chris-markus/cue-lights/controller/strings.h

// =====================================================
// Copyright (C) 2020 Christopher Markus 
// www.chrismarkus.me
// This software is licensed under the GNU GPLv3 License
// =====================================================

#ifndef STRINGS_H
#define STRINGS_H

// Strings file for controller UI
#define STR_SPLASH "Tufts Drama + Dance"

#define STR_PRESSFORMENU "Press for main menu"

#define STR_ON "On"
#define STR_OFF "Off"

#define STR_LIGHTS_STATUS "%d lights connected"

// menu strings:
#define STR_MENU_MAIN "Settings"

#define STR_BACK_BUTTON "< Back"
#define STR_CLOSE_BUTTON "X Close"

#define STR_PANEL_LIGHTS "Controller Lights"
#define STR_STATION_LIGHTS "Cue Lights"
#define STR_BRIGHTNESS "Brightness"

#define STR_STATION_I "Station %d"

#define STR_TEST_STATIONS "Test Station(s)"
#define STR_TEST_ALL_STATIONS "Test All"
#define STR_TEST_ONE_STATION "Test One"

#define STR_STBY_COLOR "Standby Color"
#define STR_GO_COLOR "Go Color"

#define STR_RED "Red"
#define STR_GREEN "Green"
#define STR_BLUE "Blue"

#define STR_NO_ISSUES "No Issues"
#define STR_ISSUES "%d issues"

#define STR_RESET "Reset Defaults"

#define STR_STATION_DISCONNECTED "Station %d last seen\n %d seconds ago"

#define STR_ABOUT "About"
#define STR_ABOUT_DESCRIPTION "Created in 2019 \nby Chris Markus\nMore information:\nchrismarkus.me/cue-lights"

#define STR_TESTING_STATION "Testing station:"

#endif
