chris-markus/cue-lights/controller/lcd_screen.cpp

// =====================================================
// Copyright (C) 2020 Christopher Markus 
// www.chrismarkus.me
// This software is licensed under the GNU GPLv3 License
// =====================================================

#include "lcd_screen.h"
#include <String.h>

LCDScreen::LCDScreen(uint16_t w, uint16_t h, TwoWire *twi, uint8_t screen_i2cAddr) 
: Adafruit_SSD1306(w, h, twi, -1) {
  i2cAddr = screen_i2cAddr;
}

void LCDScreen::init() {
  if(!begin(SSD1306_SWITCHCAPVCC, i2cAddr)) {
    Serial.println(F("SSD1306 allocation failed"));
    for(;;);
  }

  // set default text attributes
  setTextSize(1);
  setTextColor(WHITE);

  // clear the display
  clearDisplay();
}

void LCDScreen::showSplash() {
  setTextColor(WHITE);
  printCentered(STR_SPLASH);
  invertDisplay(true);
  update();
  delay(500);
  invertDisplay(false);
  update();
}

// TODO: make this work with multiple lines
int16_t LCDScreen::printCentered(const char *string, bool centerVertically, uint16_t y_offset) {
  int16_t x, y;
  uint16_t w, h;
  getTextBounds(string,0,0,&x,&y,&w,&h);
  x = (width() - w)/2;
  if (!centerVertically) {
    y = y_offset;
  }
  else {
    y = (height() - h)/2;
  }
  setCursor(x,y);
  println(string);
  return y + h;
}

int16_t LCDScreen::printCentered(const String &string, bool centerVertically, uint16_t y_offset) {
  if (string.length() != 0) {
    return printCentered(const_cast<char *>(string.c_str()), centerVertically, y_offset);
  }
  return 0;
}

// Some remapping
void LCDScreen::update() {
  display();
}

void LCDScreen::clear() {
  clearDisplay();
}
